naaeell/Mist65/mist65/pictures/20240108_131323.jpg

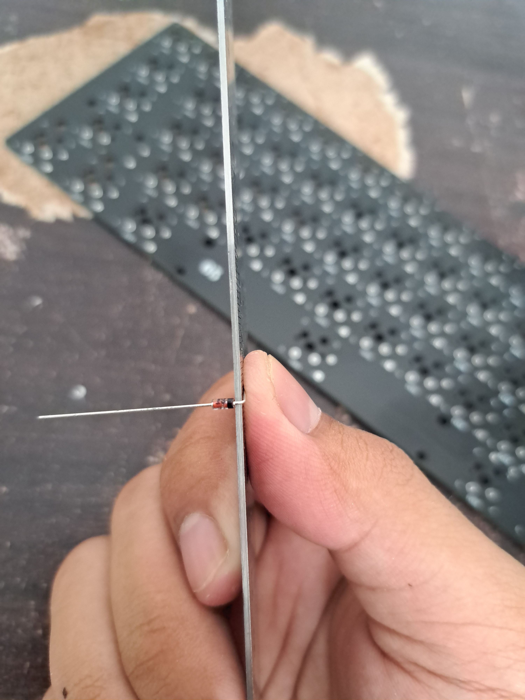
mist65/pictures/20240108_131323.jpg
