naaeell/Mist65/mist65/pictures/20240108_131418.jpg

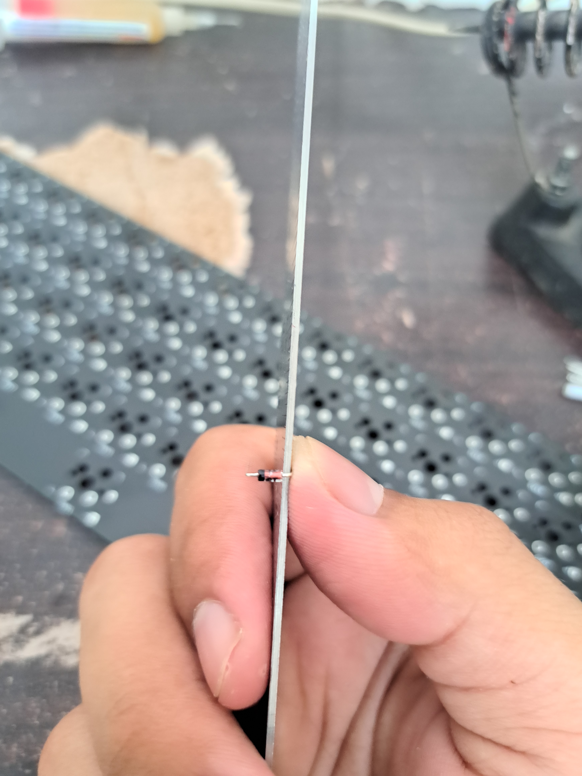
mist65/pictures/20240108_131418.jpg
