naaeell/Mist65/mist65/pictures/20240108_123602.jpg

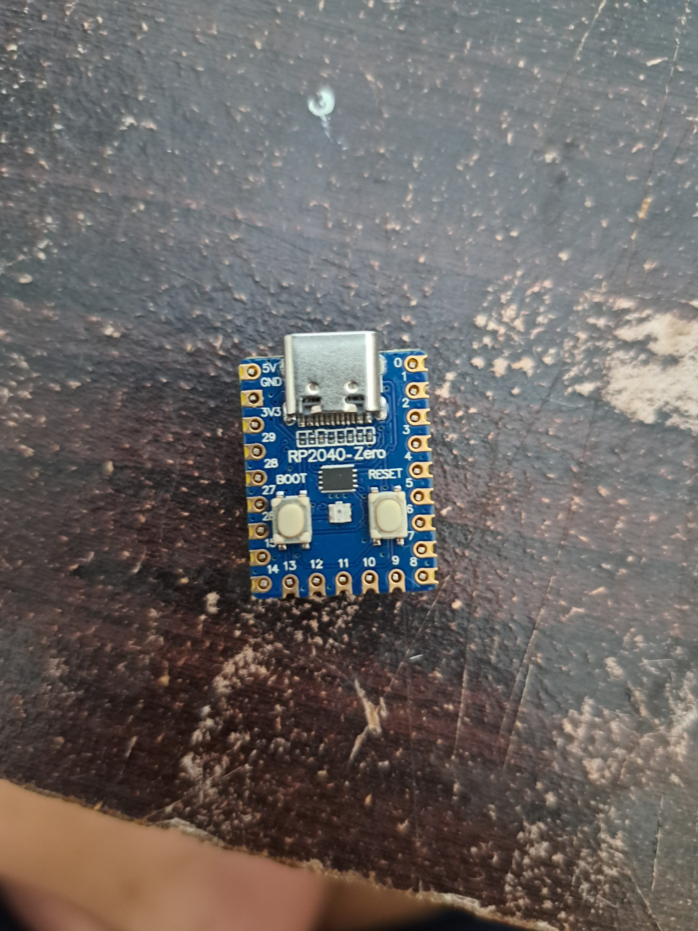
mist65/pictures/20240108_123602.jpg
