naaeell/Mist65/mist65/pictures/20240108_123809.jpg

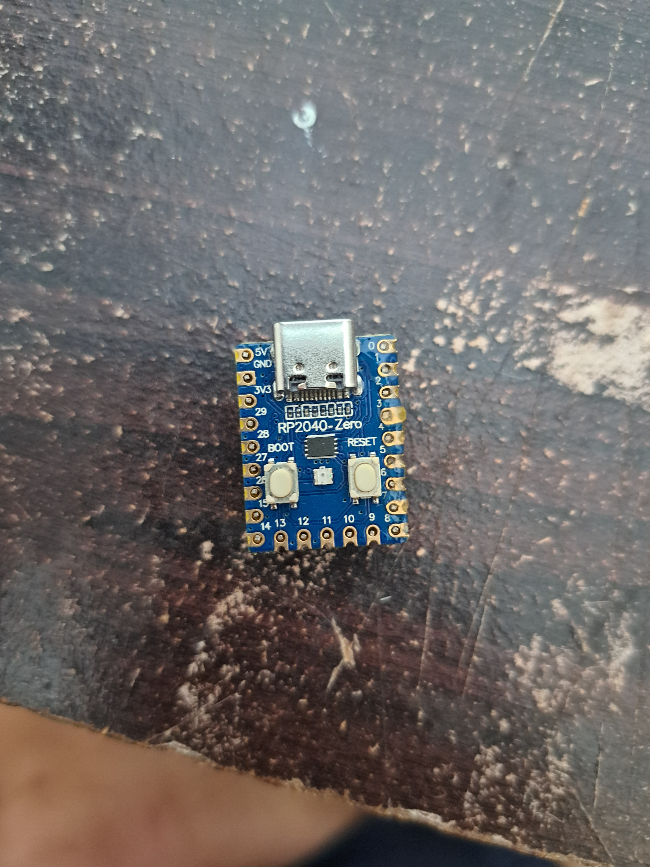
mist65/pictures/20240108_123809.jpg
