naaeell/Mist65/mist65/pictures/20240108_124805.jpg

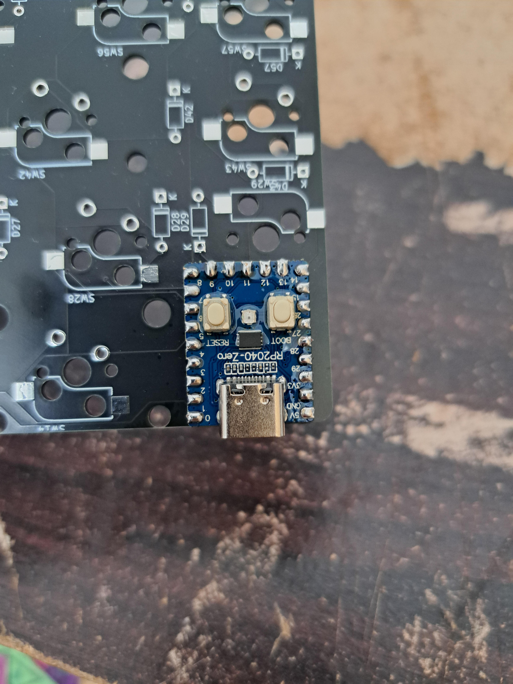
mist65/pictures/20240108_124805.jpg
