naaeell/Mist65/mist65/pictures/20240108_125505.jpg

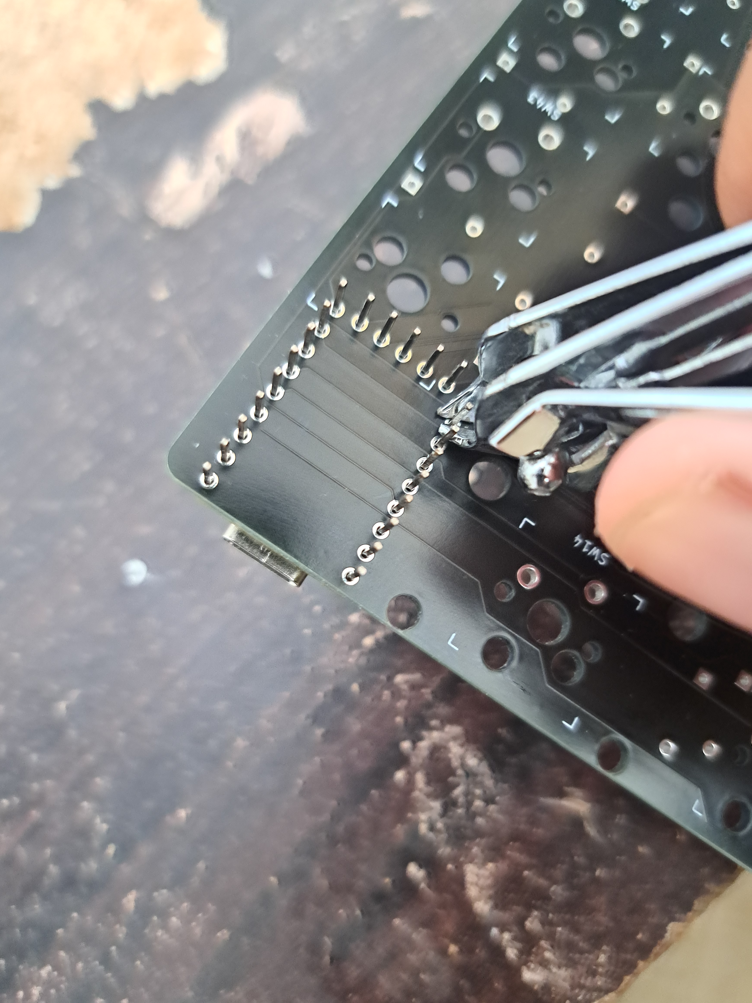
mist65/pictures/20240108_125505.jpg
