naaeell/Mist65/mist65/pictures/20240108_130131.jpg

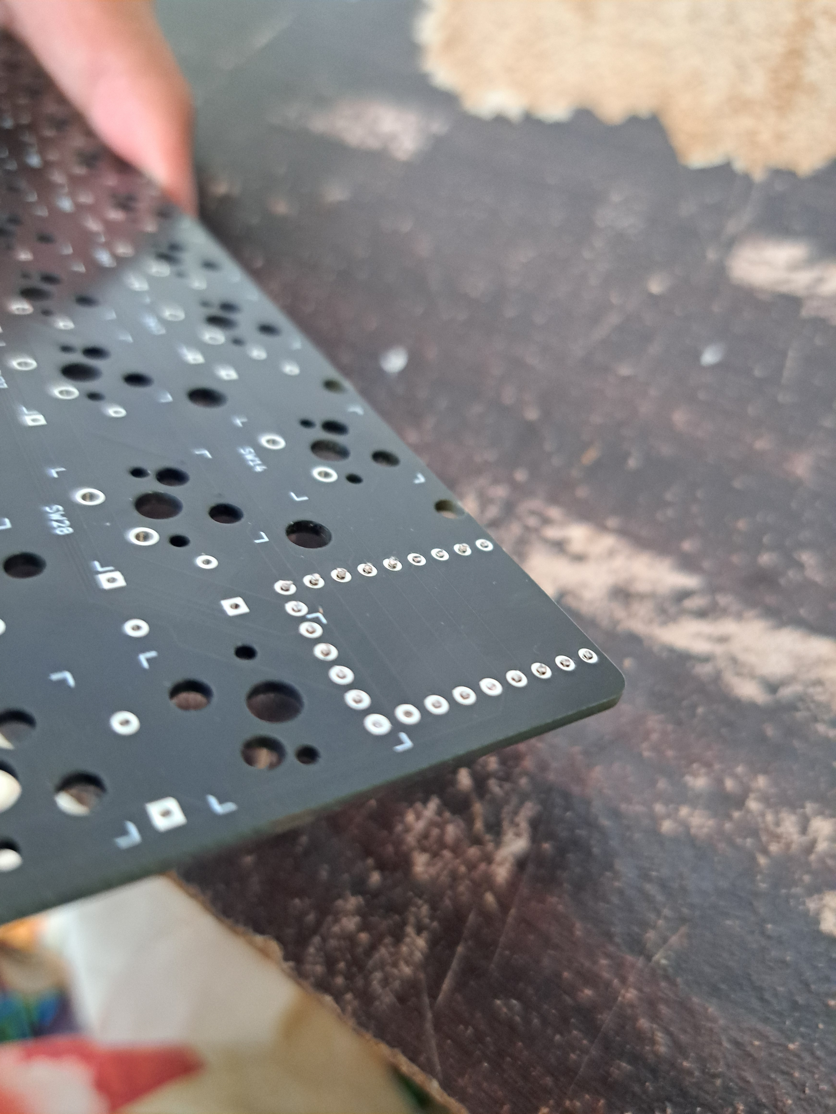
mist65/pictures/20240108_130131.jpg
